zsoltibaba37/Canon_Control_board/pics/IMG_20210122_155335.jpg

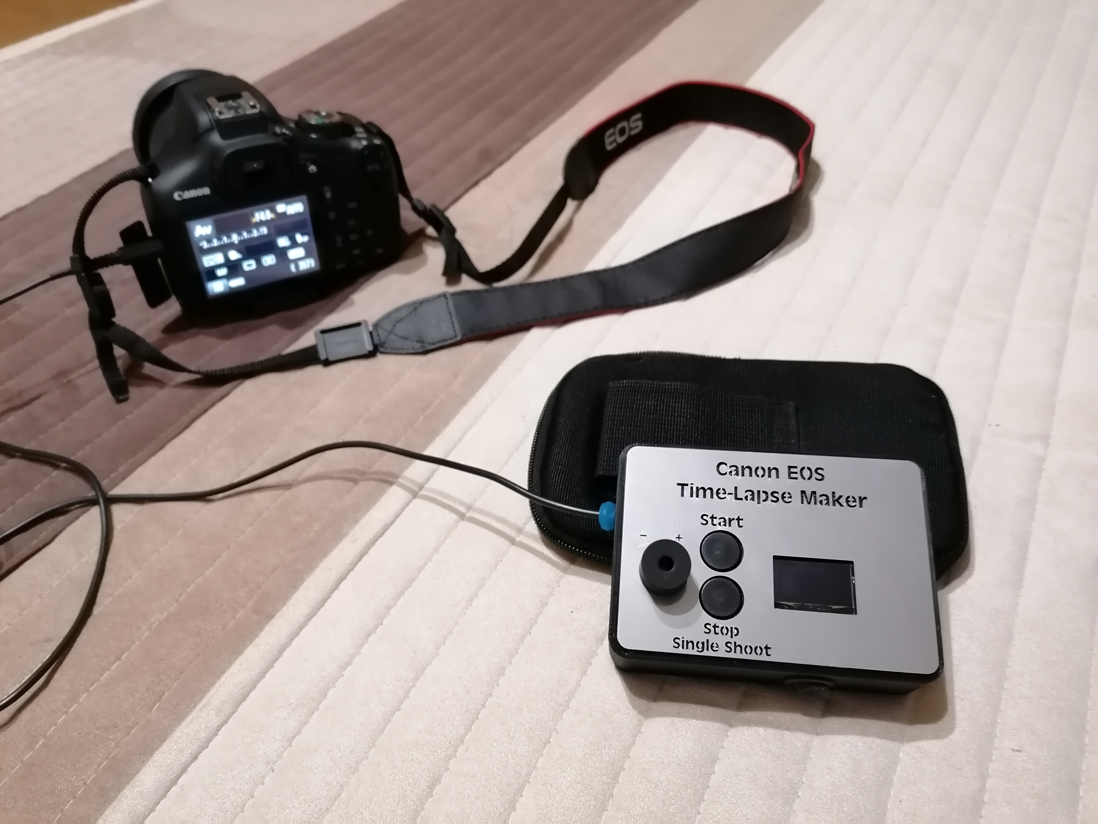
pics/IMG_20210122_155335.jpg
