zsoltibaba37/Canon_Control_board/pics/IMG_20210122_155450.jpg

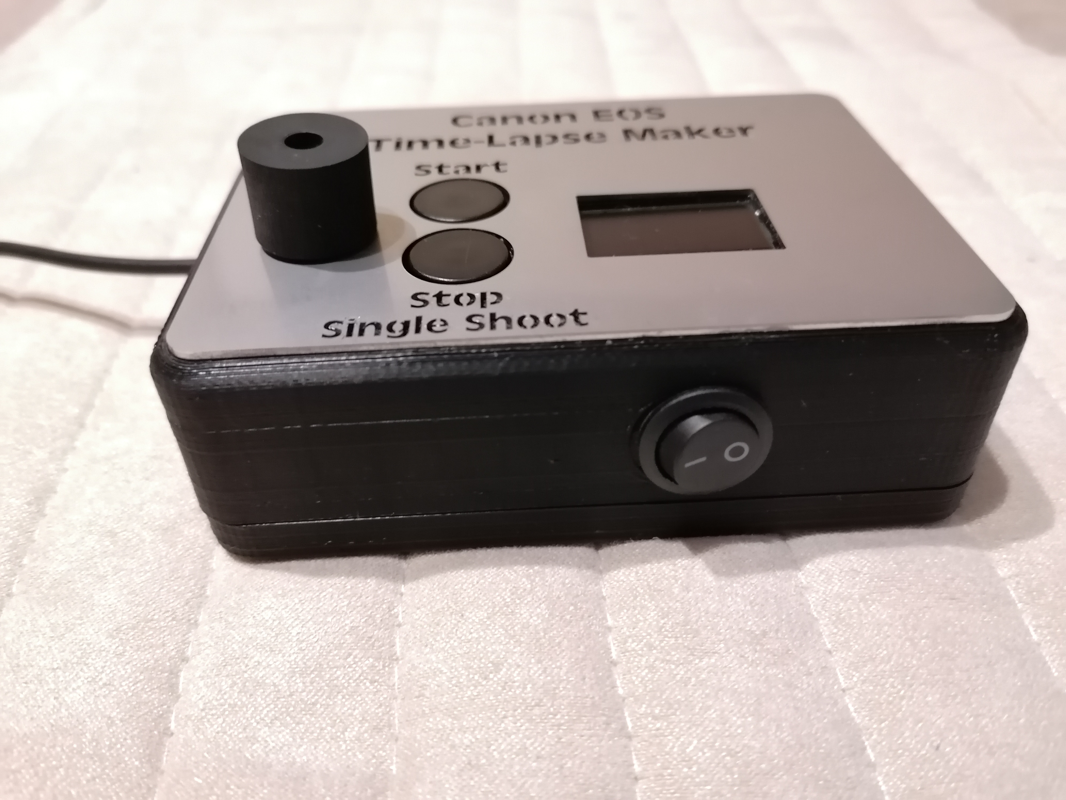
pics/IMG_20210122_155450.jpg
