zsoltibaba37/Canon_Control_board/pics/IMG_20210122_155505.jpg

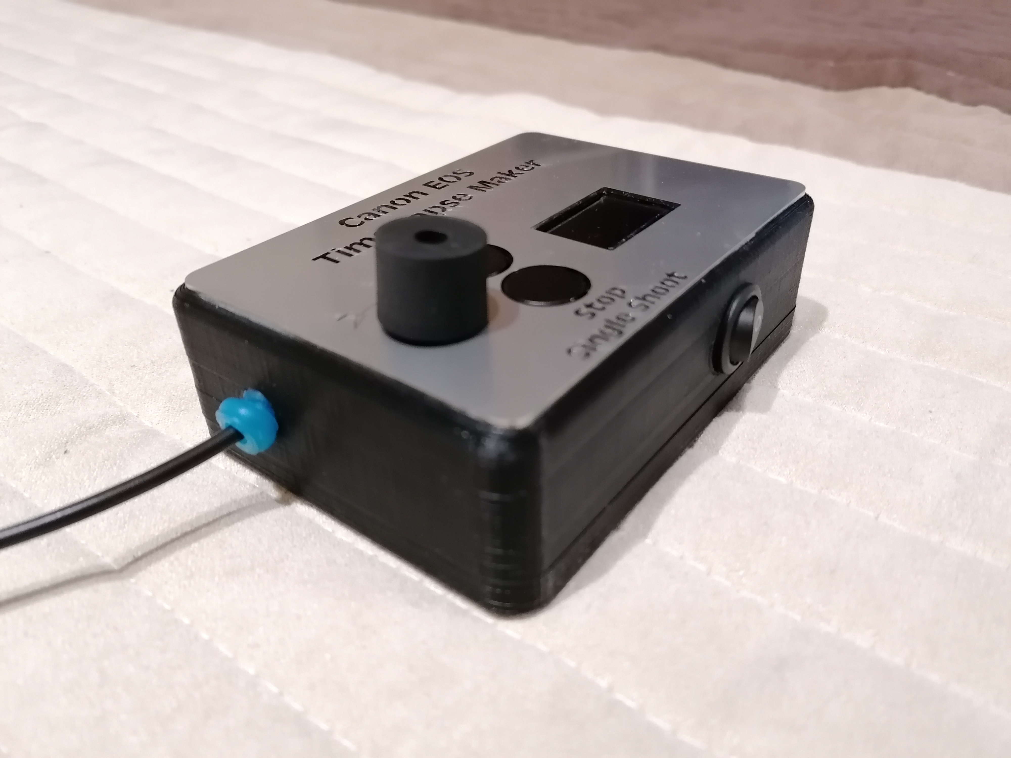
pics/IMG_20210122_155505.jpg
