zsoltibaba37/Canon_Control_board/pics/IMG_20210122_155521.jpg

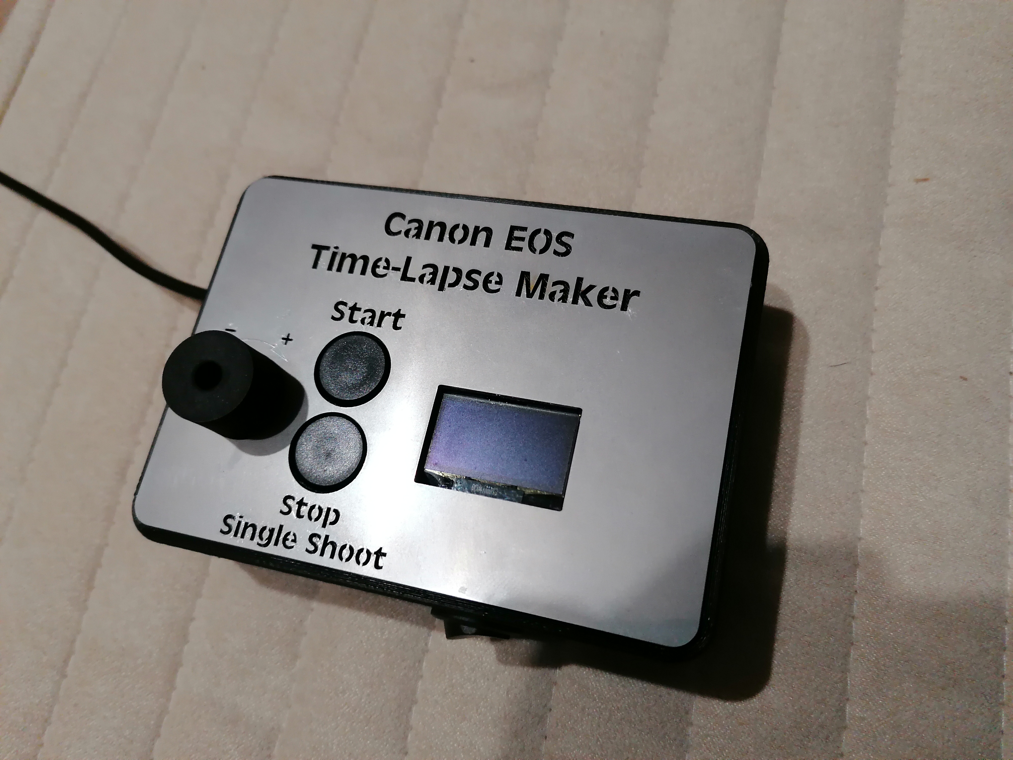
pics/IMG_20210122_155521.jpg
